slazav/ptlogger/box3d/pics/_1865.jpg

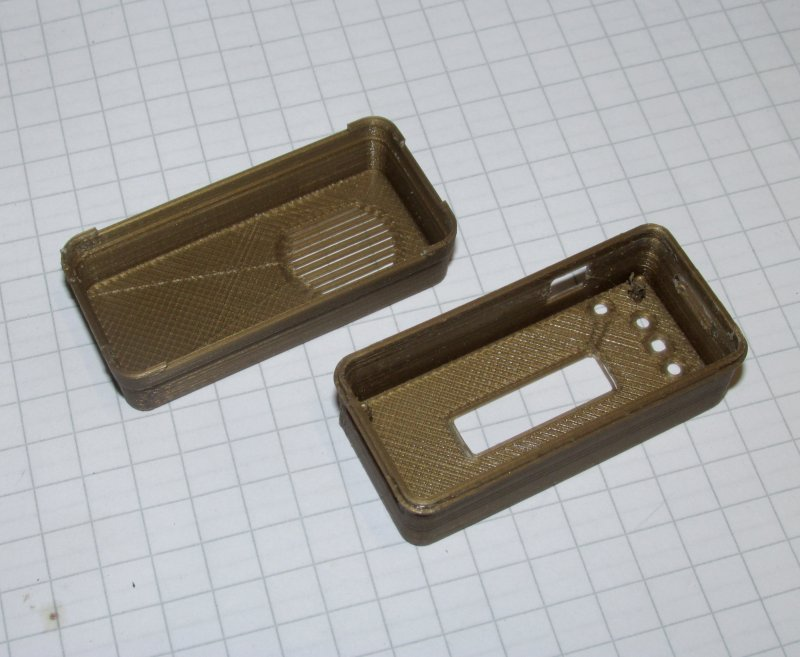
box3d/pics/_1865.jpg
