slazav/ptlogger/box3d/pics/_1867.jpg

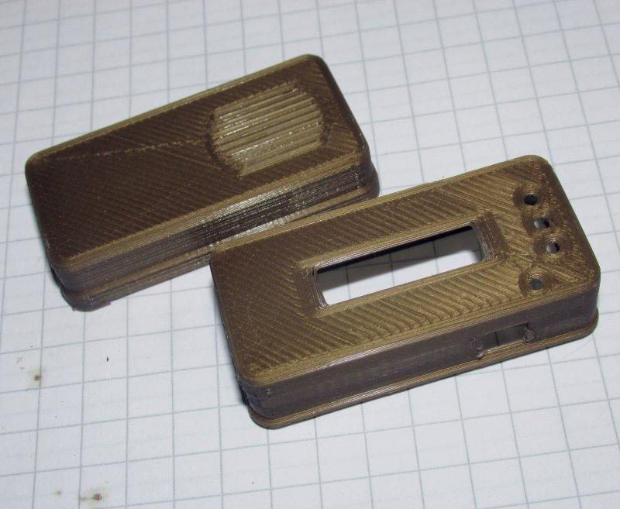
box3d/pics/_1867.jpg
