slazav/ptlogger/pcb/pics/_1813.jpg

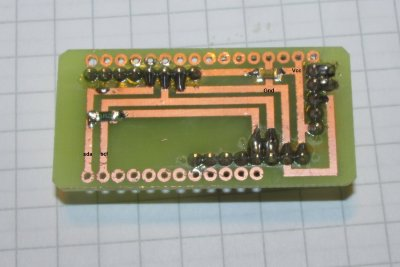
pcb/pics/_1813.jpg
