slazav/ptlogger/pcb/pics/_1821.jpg

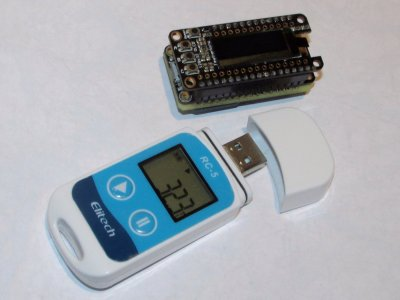
pcb/pics/_1821.jpg
