slazav/ptlogger/pcb/pics/_1824.jpg

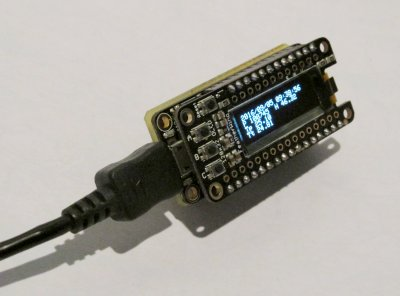
pcb/pics/_1824.jpg
