slazav/ptlogger/pcb/pics/_1825.jpg

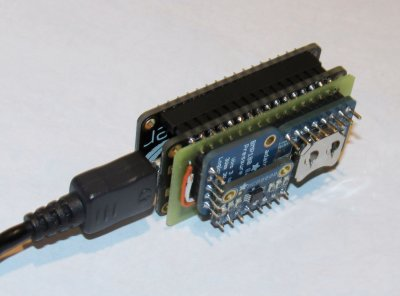
pcb/pics/_1825.jpg
